DreaM117er/MagWave44/pics/all2.png

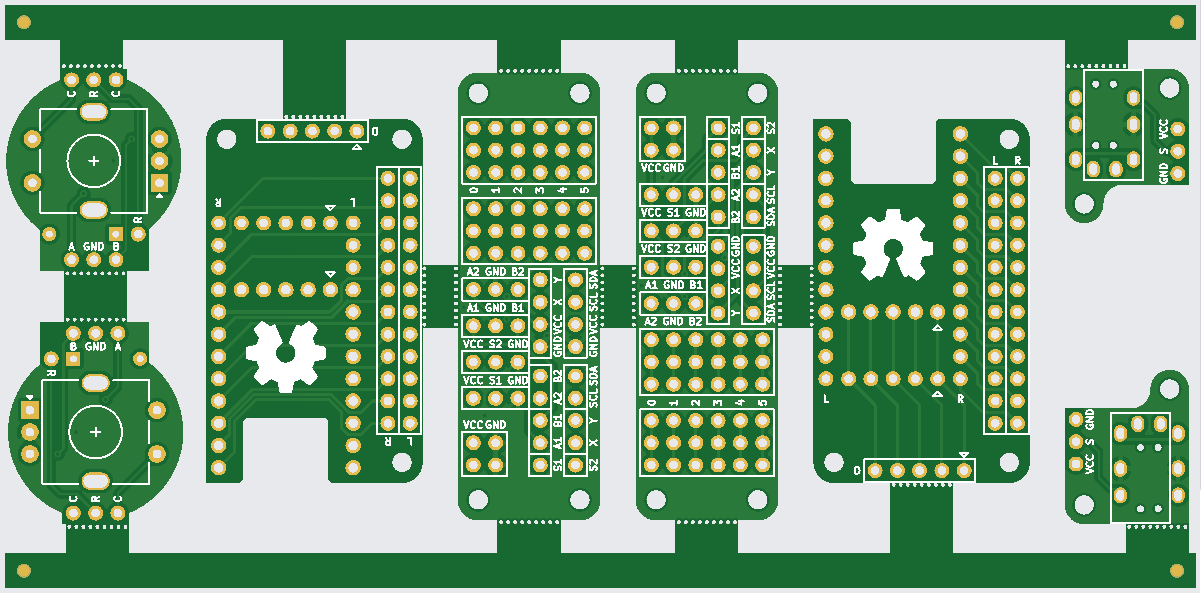
pics/all2.png
