DreaM117er/MagWave44/pics/mdl01.png

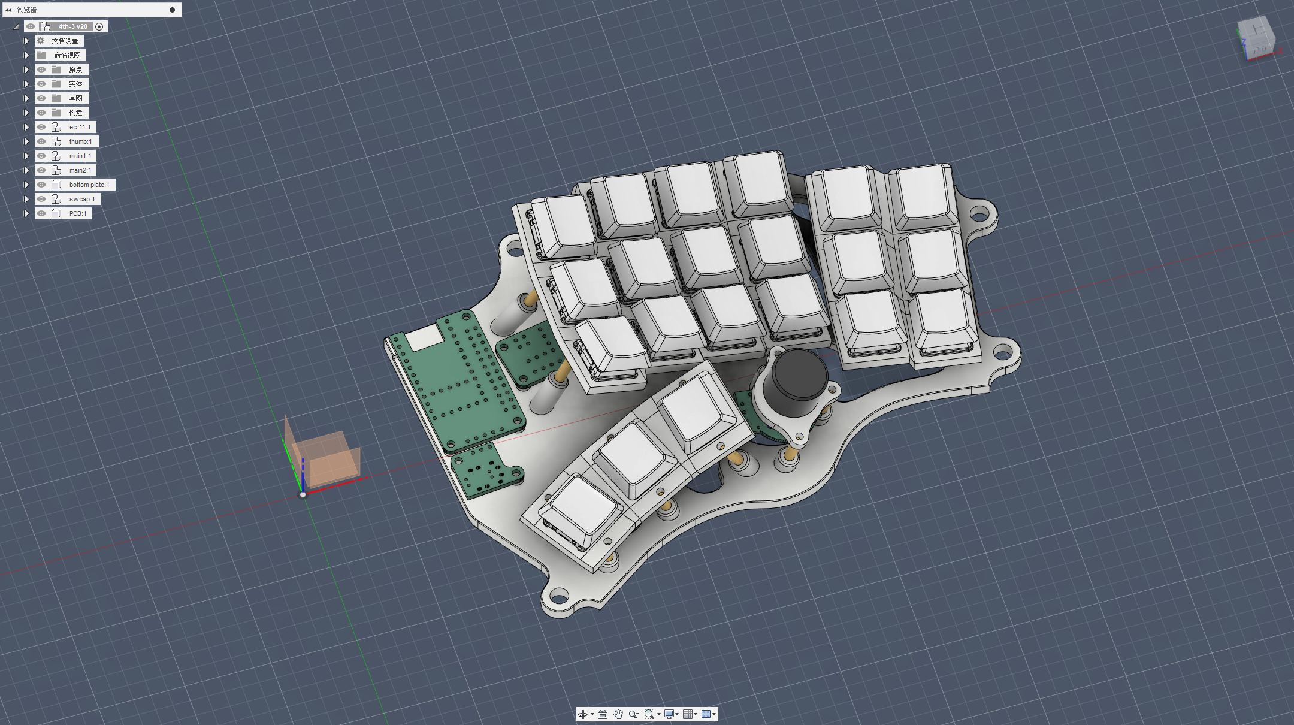
pics/mdl01.png
