DreaM117er/MagWave44/files/pcb/main.kicad_sch

## KiCad design files/pcb/main.kicad_sch (2024-01-24)

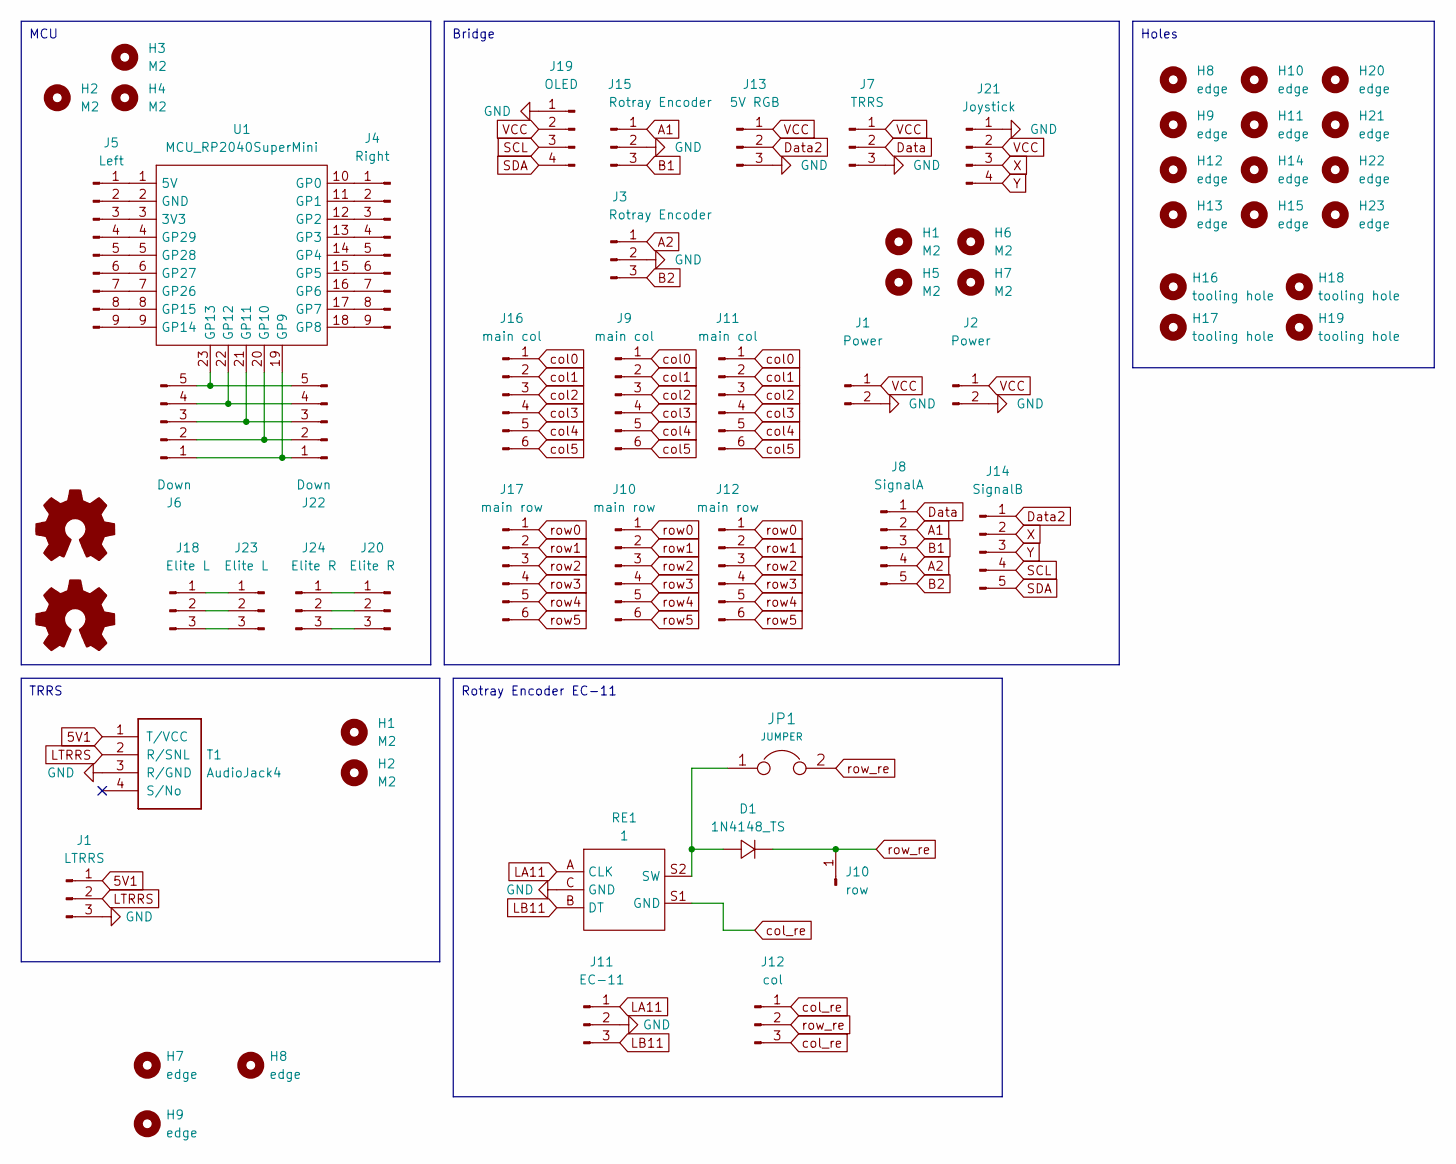
[picture p90: schematic main.kicad_sch]

Parts:
D1: 1N4148_TS; D_DO-35_SOD27_P7.62mm_Horizontal
H1, H2, H3, H4, H5, H6: M2; MountingHole_2.2mm_M2
H7, H8, H9, H10, H11, H12, H13, H14, H15, H20, H21, H22, H23: edge; Breakaway_Tabs
H16, H17, H18, H19: tooling hole; tooling_hole
J1: LTRRS; PinHeader_1x03_P2.54mm_Vertical
J2: Power; PinHeader_1x02_P2.54mm_Vertical
J3, J15: Rotray Encoder; PinHeader_1x03_P2.54mm_Vertical
J4: Right; PinHeader_1x09_P2.54mm_Vertical
J5: Left; PinHeader_1x09_P2.54mm_Vertical
J6, J22: Down; PinHeader_1x05_P2.54mm_Vertical
J7: TRRS; PinHeader_1x03_P2.54mm_Vertical
J8: SignalA; PinHeader_1x05_P2.54mm_Vertical
J9, J11, J16: main col; PinHeader_1x06_P2.54mm_Vertical
J10, J12, J17: main row; PinHeader_1x06_P2.54mm_Vertical
J13: 5V RGB; PinHeader_1x03_P2.54mm_Vertical
J14: SignalB; PinHeader_1x05_P2.54mm_Vertical
J18, J23: Elite L; PinHeader_1x03_P2.54mm_Vertical
J19: OLED; PinHeader_1x04_P2.54mm_Vertical
J20, J24: Elite R; PinHeader_1x03_P2.54mm_Vertical
J21: Joystick; PinHeader_1x04_P2.54mm_Vertical
JP1: JUMPER; SolderJumper-2_P1.3mm_Open_TrianglePad1.0x1.5mm
RE1: 1; RotaryEncoder_EC11
T1: AudioJack4; TRRS-PJ-320A, dual side x2
U1: MCU_RP2040SuperMini

Connections:
5V1: J1.1, T1.1 (T/VCC)
A1: J8.2, J15.1
A2: J3.1, J8.4
B1: J8.3, J15.3
B2: J3.3, J8.5
Data: J7.2, J8.1
Data2: J13.2, J14.1
GND: J1.2, J1.3, J2.2, J3.2, J7.3, J11.2, J13.3, J15.2, J19.1, J21.1, RE1.C (GND), T1.3 (R/GND)
LA11: J11.1, RE1.A (CLK)
LB11: J11.3, RE1.B (DT)
LTRRS: J1.2, T1.2 (R/SNL)
unnamed: D1.2, JP1.1, RE1.S2 (SW)
unnamed: J4.1, U1.10 (GP0)
unnamed: J4.2, U1.11 (GP1)
unnamed: J4.3, U1.12 (GP2)
unnamed: J4.4, U1.13 (GP3)
unnamed: J4.5, U1.14 (GP4)
unnamed: J4.6, U1.15 (GP5)
unnamed: J4.7, U1.16 (GP6)
unnamed: J4.8, U1.17 (GP7)
unnamed: J4.9, U1.18 (GP8)
unnamed: J5.1, U1.1 (5V)
unnamed: J5.2, U1.2 (GND)
unnamed: J5.3, U1.3 (3V3)
unnamed: J5.4, U1.4 (GP29)
unnamed: J5.5, U1.5 (GP28)
unnamed: J5.6, U1.6 (GP27)
unnamed: J5.7, U1.7 (GP26)
unnamed: J5.8, U1.8 (GP15)
unnamed: J5.9, U1.9 (GP14)
unnamed: J18.1, J23.1
unnamed: J18.2, J23.2
unnamed: J18.3, J23.3
unnamed: J20.1, J24.1
unnamed: J20.2, J24.2
unnamed: J20.3, J24.3
unnamed: J6.1, J22.1, U1.19 (GP9)
unnamed: J6.2, J22.2, U1.20 (GP10)
unnamed: J6.3, J22.3, U1.21 (GP11)
unnamed: J6.4, J22.4, U1.22 (GP12)
unnamed: J6.5, J22.5, U1.23 (GP13)
SCL: J14.4, J19.3
SDA: J14.5, J19.4
VCC: J1.1, J2.1, J7.1, J13.1, J19.2, J21.2
X: J14.2, J21.3
Y: J14.3, J21.4
col0: J9.1, J11.1, J16.1
col1: J9.2, J11.2, J16.2
col2: J9.3, J11.3, J16.3
col3: J9.4, J11.4, J16.4
col4: J9.5, J11.5, J16.5
col5: J9.6, J11.6, J16.6
col_re: J12.1, J12.3, RE1.S1 (GND)
row0: J10.1, J12.1, J17.1
row1: J10.2, J12.2, J17.2
row2: J10.3, J12.3, J17.3
row3: J10.4, J12.4, J17.4
row4: J10.5, J12.5, J17.5
row5: J10.6, J12.6, J17.6
row_re: D1.1, J10.1, J12.2, JP1.2

Notes on the sheet:
TRRS
Bridge
MCU
Rotray Encoder EC-11
Holes
